Archive-663/samyang7_5mm/ASSETS/PRODUCT/sam7_5_product (2).jpg

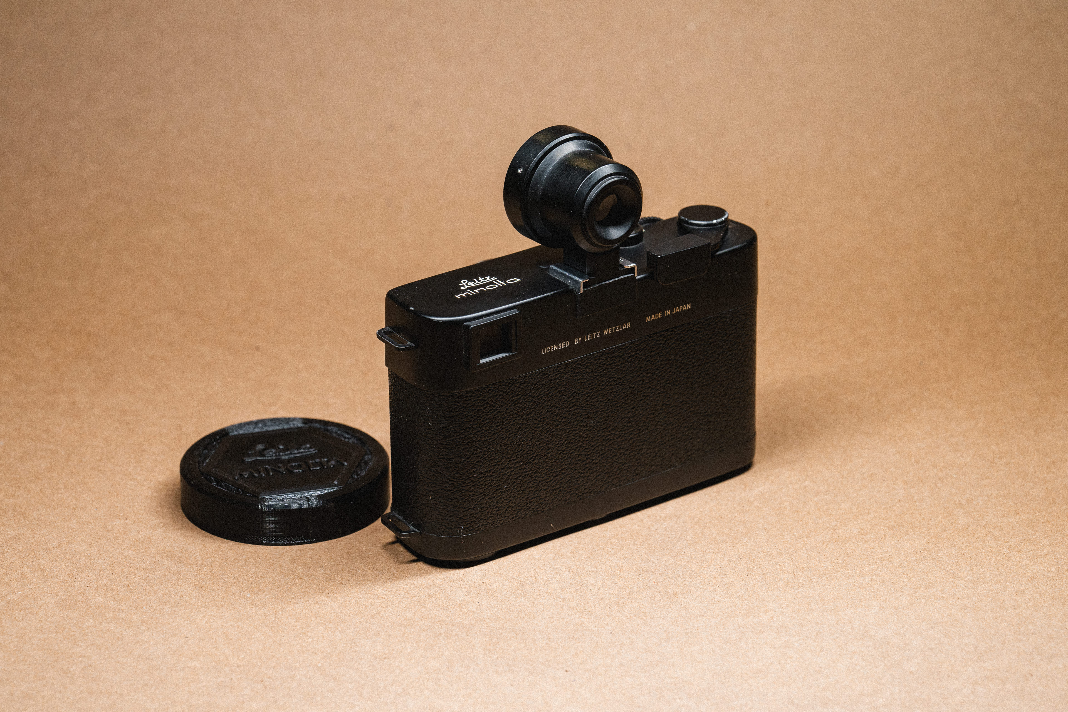
ASSETS/PRODUCT/sam7_5_product (2).jpg
