Archive-663/samyang7_5mm/ASSETS/PRODUCT/sam7_5_product (7).jpg

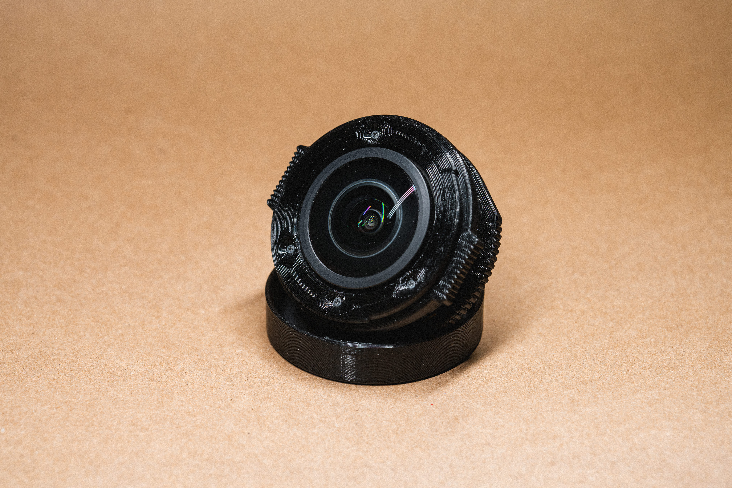
ASSETS/PRODUCT/sam7_5_product (7).jpg
