Archive-663/samyang7_5mm/ASSETS/PRODUCT/sam7_5_product (9).jpg

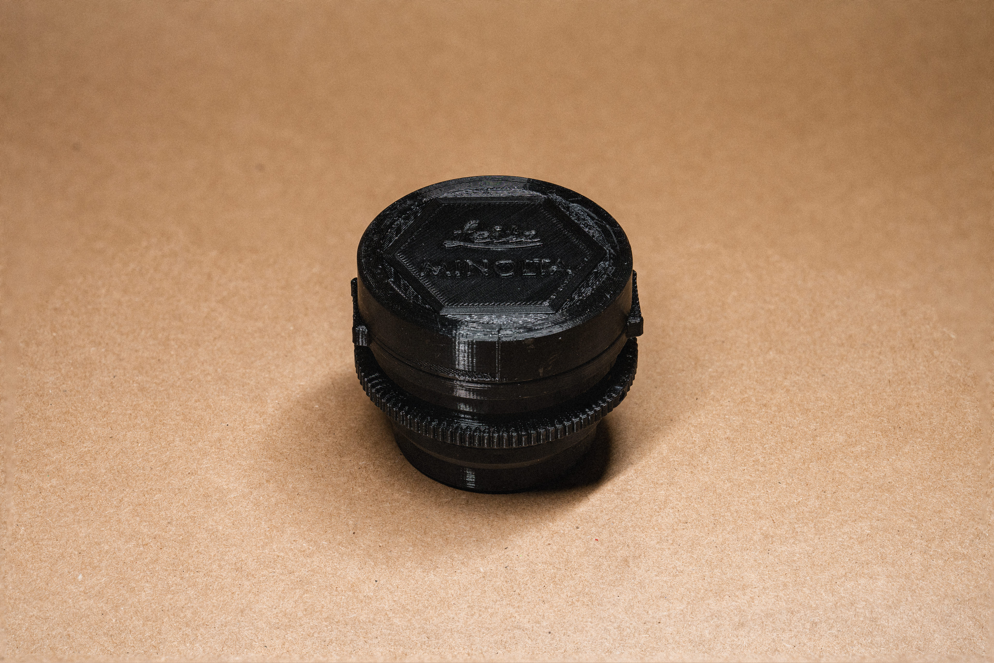
ASSETS/PRODUCT/sam7_5_product (9).jpg
