Archive-663/samyang7_5mm/ASSETS/PRODUCT/sam7_5_product (10).jpg

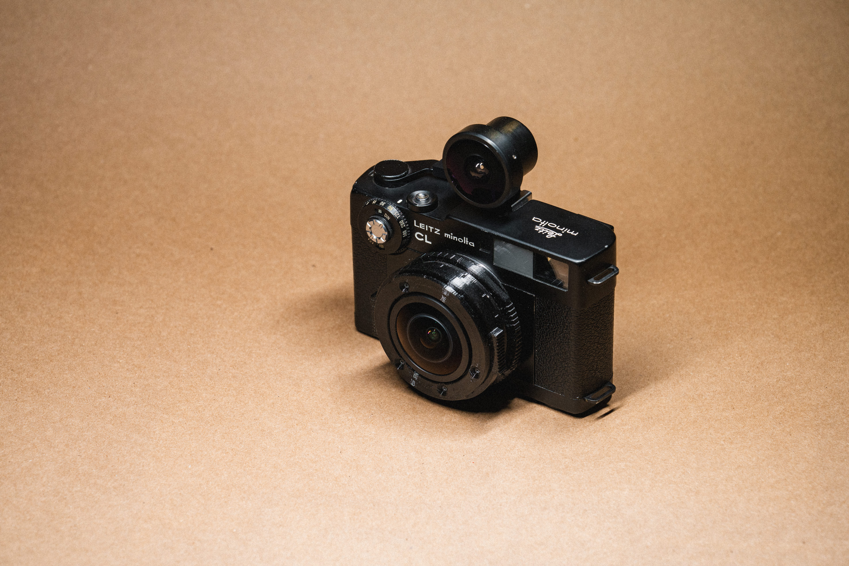
ASSETS/PRODUCT/sam7_5_product (10).jpg
