Archive-663/samyang7_5mm/ASSETS/SAMPLE/sam7_5_sample (22).jpg

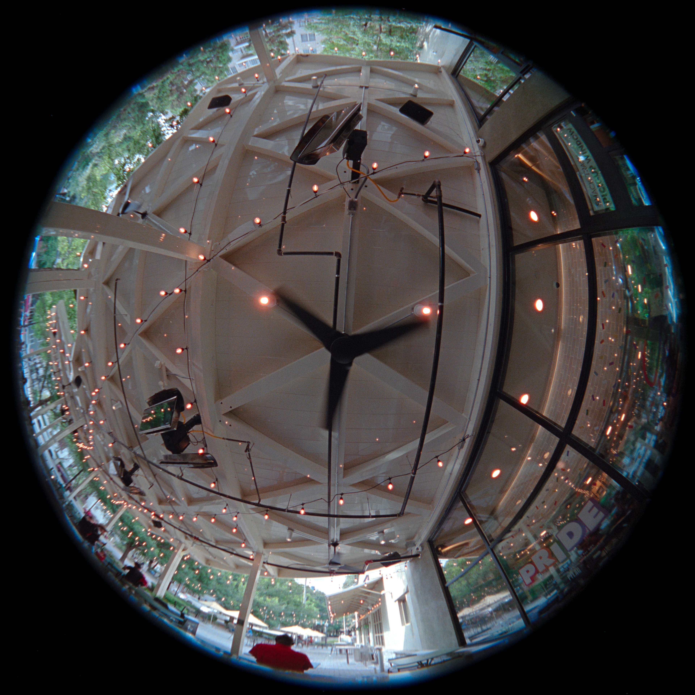
ASSETS/SAMPLE/sam7_5_sample (22).jpg
