Archive-663/samyang7_5mm/viewFinder/STL/Lemuro Fisheye/forPrint/sam7_5_MFT-LM_viewFinderCap_lemuroFisheye_forPrint.stl

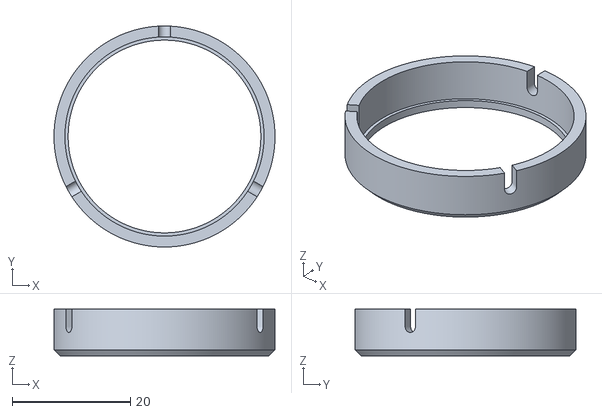
[picture p45: CAD file, 2023-12-08]
viewFinder/STL/Lemuro Fisheye/forPrint/sam7_5_MFT-LM_viewFinderCap_lemuroFisheye_forPrint.stl
37.4 x 37.4 x 7.88
