Archive-663/samyang7_5mm/viewFinder/STL/Standard/sam7_5_MFT-LM_viewFinderColdShoe.stl

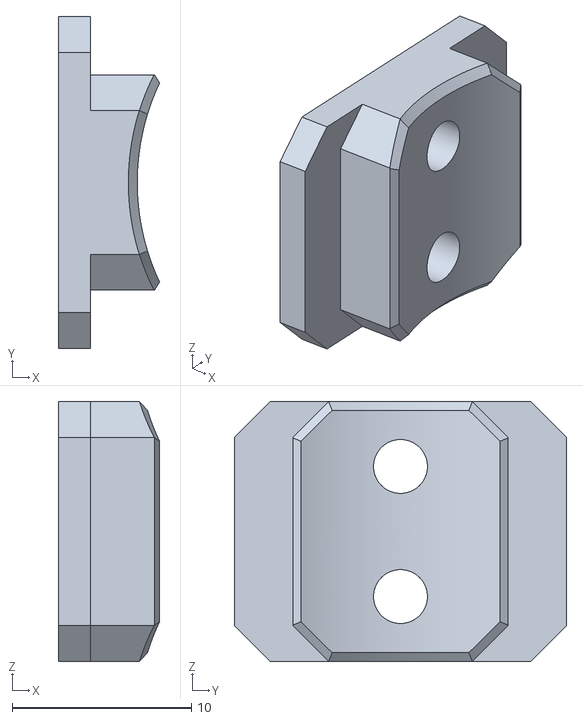
[picture p46: CAD file, 2023-12-08]
viewFinder/STL/Standard/sam7_5_MFT-LM_viewFinderColdShoe.stl
5.64 x 18.5 x 14.5
