Archive-663/samyang7_5mm/sam7_5_MFT-LM_rehousing/STEP/sam7_5_MFT-LM_rearCap_LM.stp

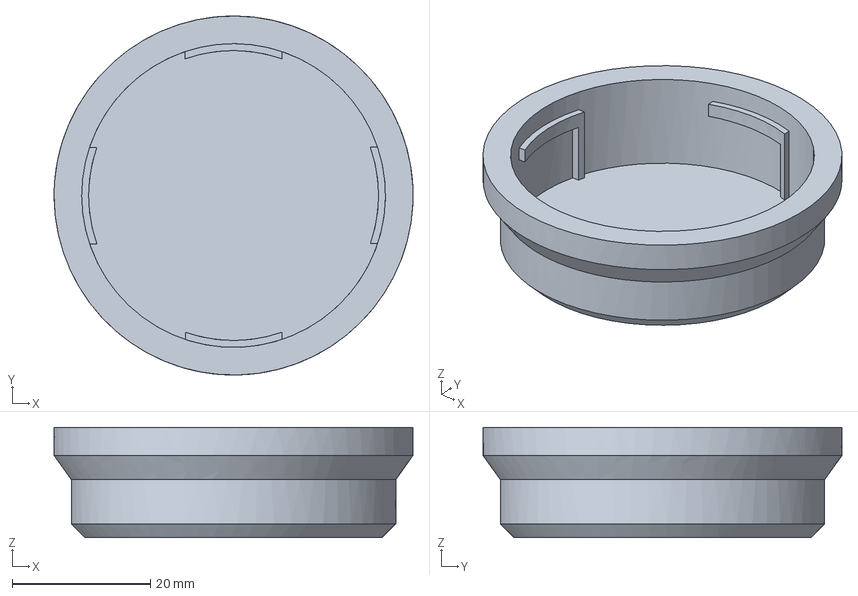
[picture p47: CAD file, 2023-12-08]
sam7_5_MFT-LM_rehousing/STEP/sam7_5_MFT-LM_rearCap_LM.stp
52.0 x 52.0 x 16.0 mm
