Archive-663/samyang7_5mm/viewFinder/STEP/Death Lens Fisheye/forPrint/sam7_5_viewFinderColdShoe_deathLensFisheye_forPrint.stp

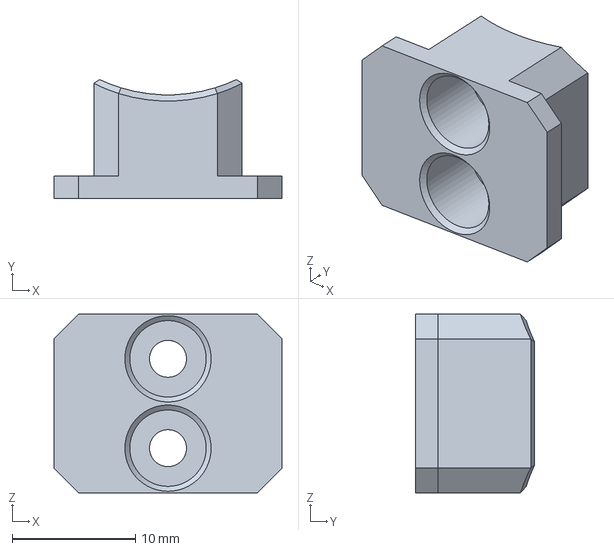
[picture p48: CAD file, 2023-12-08]
viewFinder/STEP/Death Lens Fisheye/forPrint/sam7_5_viewFinderColdShoe_deathLensFisheye_forPrint.stp
18.5 x 9.64 x 14.5 mm
