Archive-663/samyang7_5mm/viewFinder/STEP/Lemuro Fisheye/forCNC/sam7_5_viewFinderBody_lemuroFisheye_forCNC.stp

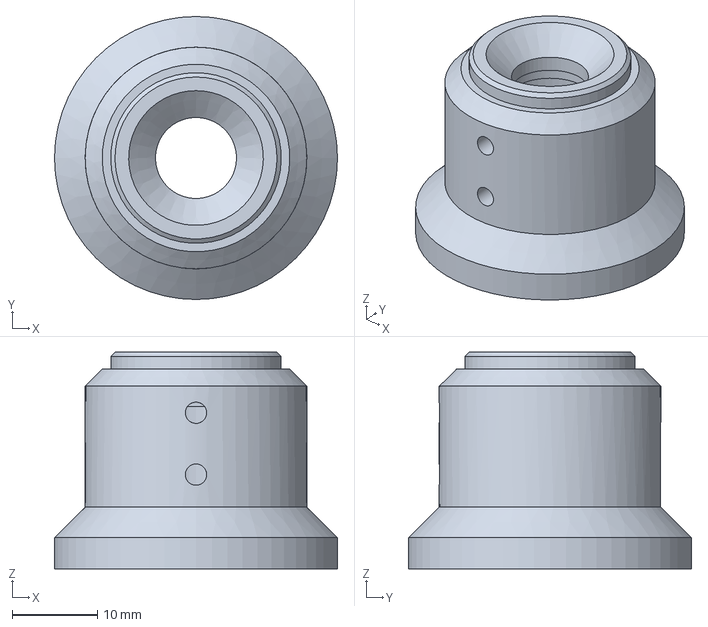
[picture p49: CAD file, 2023-12-08]
viewFinder/STEP/Lemuro Fisheye/forCNC/sam7_5_viewFinderBody_lemuroFisheye_forCNC.stp
33.2 x 33.2 x 25.5 mm
