Archive-663/samyang7_5mm/viewFinder/STEP/Lemuro Fisheye/forPrint/sam7_5_viewFinderColdShoe_lemuroFisheye_forPrint.stp

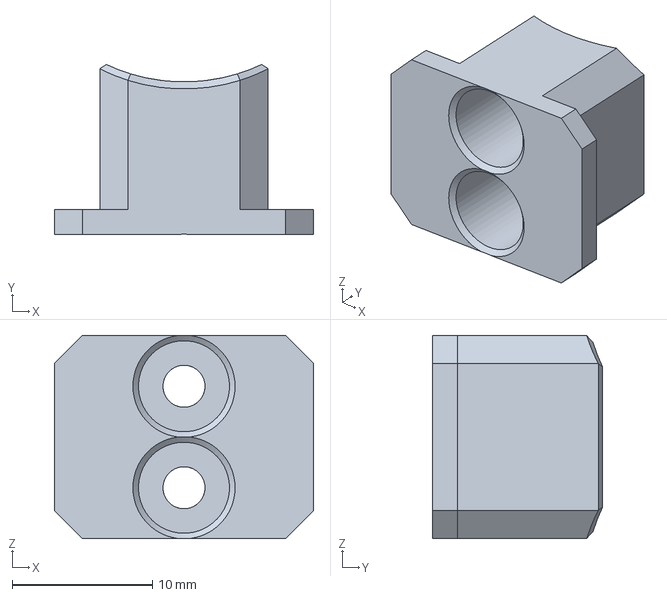
[picture p50: CAD file, 2023-12-08]
viewFinder/STEP/Lemuro Fisheye/forPrint/sam7_5_viewFinderColdShoe_lemuroFisheye_forPrint.stp
18.5 x 12.1 x 14.5 mm
