Archive-663/samyang7_5mm/viewFinder/STEP/Standard/sam7_5_viewFinderBody_standard.stp

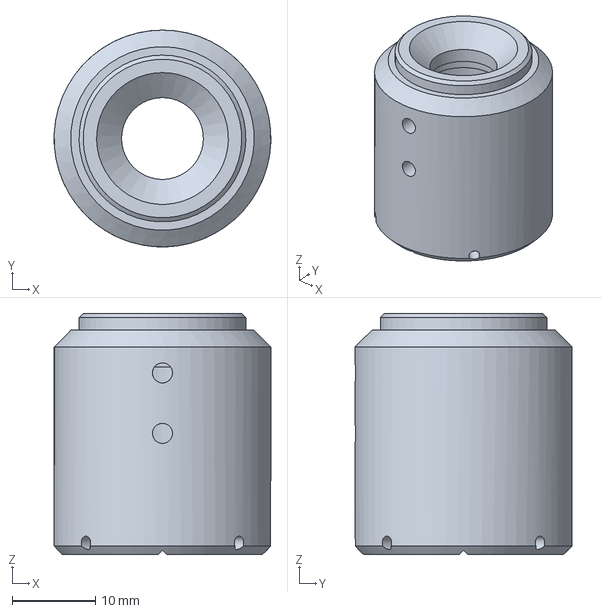
[picture p51: CAD file, 2023-12-08]
viewFinder/STEP/Standard/sam7_5_viewFinderBody_standard.stp
26.0 x 26.0 x 28.9 mm
