Archive-663/samyang7_5mm/viewFinder/STL/Standard/sam7_5_MFT-LM_viewFinder_standard.3mf

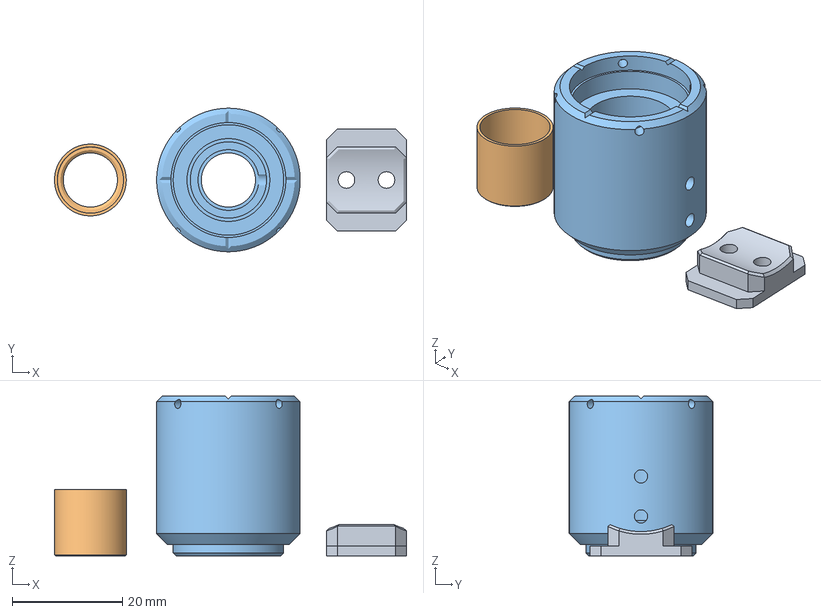
[picture p52: CAD file, 2023-12-08]
viewFinder/STL/Standard/sam7_5_MFT-LM_viewFinder_standard.3mf
63.7 x 26.0 x 28.9 mm
sam7_5_MFT-LM_viewFinderColdShoe.stl
sam7_5_MFT-LM_viewFinder_collar_glassElement.stl
sam7_5_MFT-LM_viewFinderBody_standard.stl
