Archive-663/samyang7_5mm/sam7_5_MFT-LM_rehousing/STEP/sam7_5_MFT-LM_facePlate.stp

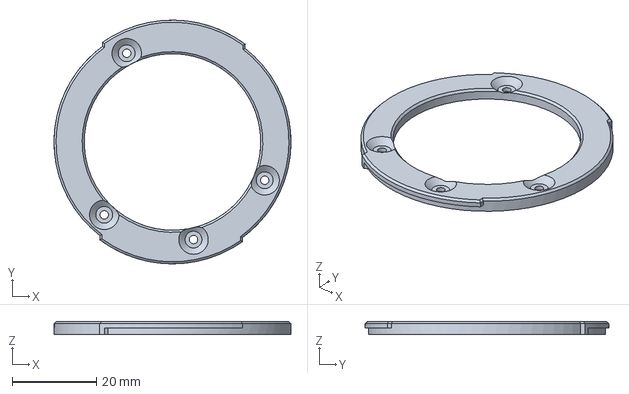
[picture p53: CAD file, 2023-12-08]
sam7_5_MFT-LM_rehousing/STEP/sam7_5_MFT-LM_facePlate.stp
56.4 x 58.0 x 3.10 mm
