Archive-663/samyang7_5mm/viewFinder/STL/Death Lens Fisheye/forPrint/sam7_5_MFT-LM_viewFinderBody_deathLensFisheye_forPrint.stl

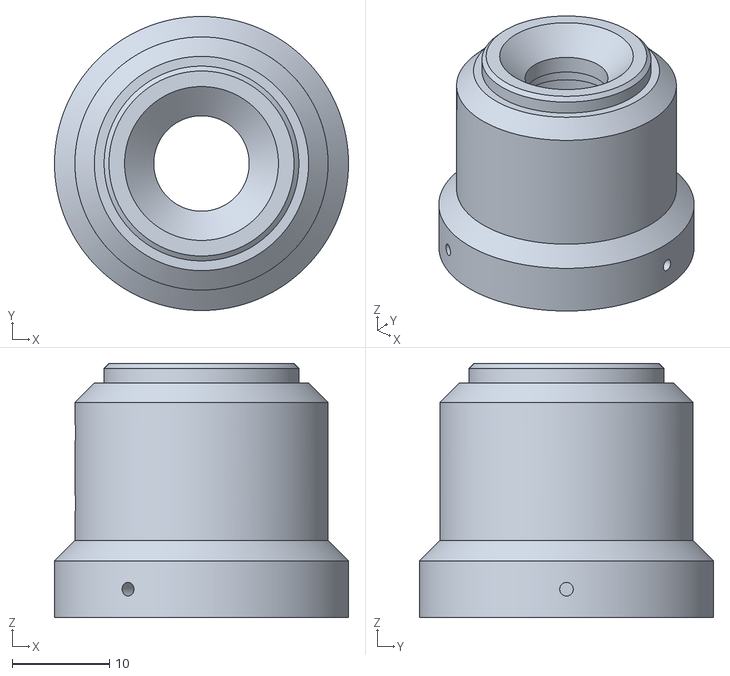
[picture p54: CAD file, 2023-12-08]
viewFinder/STL/Death Lens Fisheye/forPrint/sam7_5_MFT-LM_viewFinderBody_deathLensFisheye_forPrint.stl
30.2 x 30.2 x 26.1
