Archive-663/samyang7_5mm/viewFinder/STL/Lemuro Fisheye/forPrint/sam7_5_MFT-LM_viewFinder_lemuroFisheye.3mf

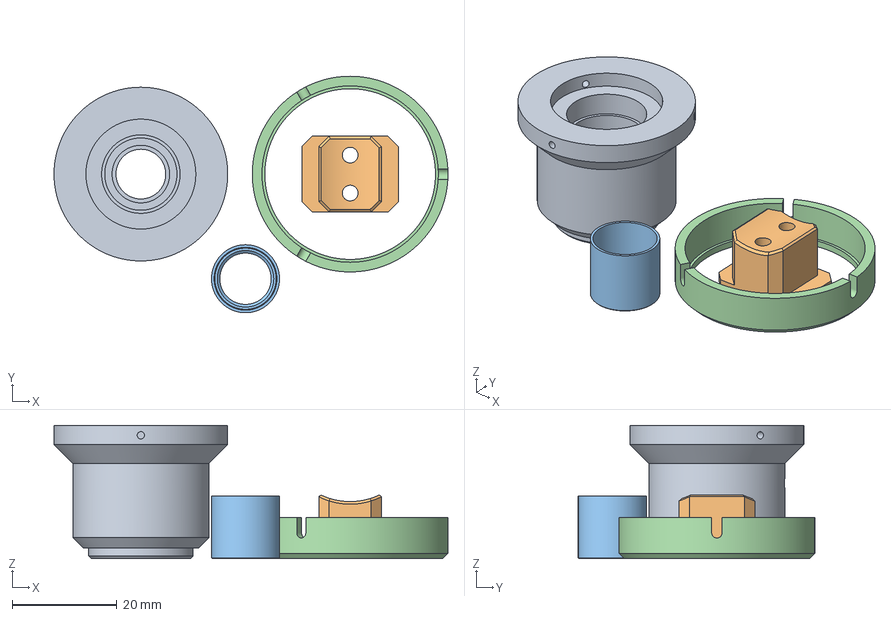
[picture p55: CAD file, 2023-12-08]
viewFinder/STL/Lemuro Fisheye/forPrint/sam7_5_MFT-LM_viewFinder_lemuroFisheye.3mf
75.3 x 45.2 x 25.4 mm
sam7_5_MFT-LM_viewFinderBody_lemuroFisheye_forPrint.stl
sam7_5_MFT-LM_viewFinderColdShoe_lemuroFisheye_forPrint.stl
sam7_5_MFT-LM_viewFinder_collar_glassElement.stl
sam7_5_MFT-LM_viewFinderCap_lemuroFisheye_forPrint.stl
