Archive-663/samyang7_5mm/sam7_5_MFT-LM_rehousing/STEP/sam7_5_MFT-LM_apertureArmBuck.stp

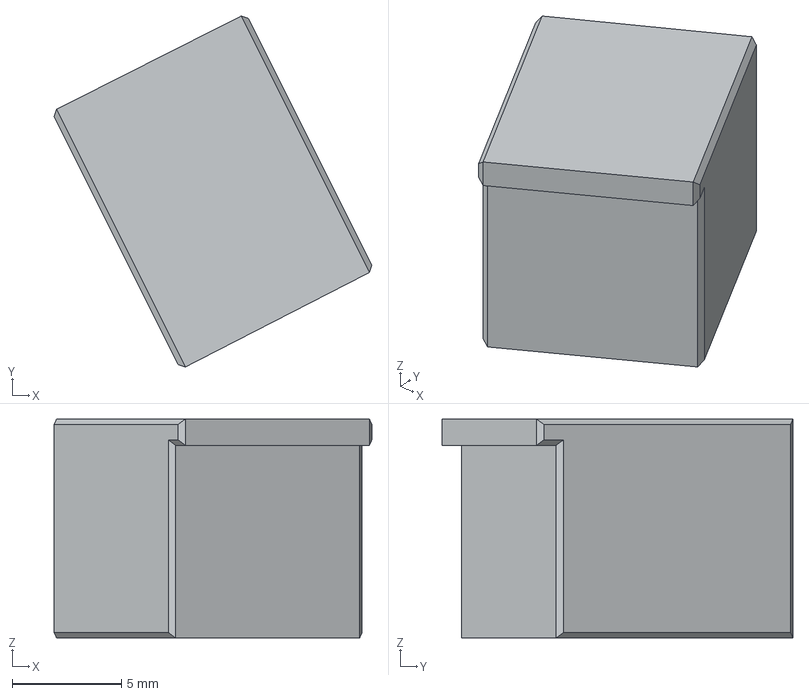
[picture p56: CAD file, 2023-12-08]
sam7_5_MFT-LM_rehousing/STEP/sam7_5_MFT-LM_apertureArmBuck.stp
14.5 x 16.0 x 10.00 mm
