Archive-663/samyang7_5mm/viewFinder/STL/Death Lens Fisheye/forPrint/sam7_5_MFT-LM_viewFinder_deathLensFisheye.3mf

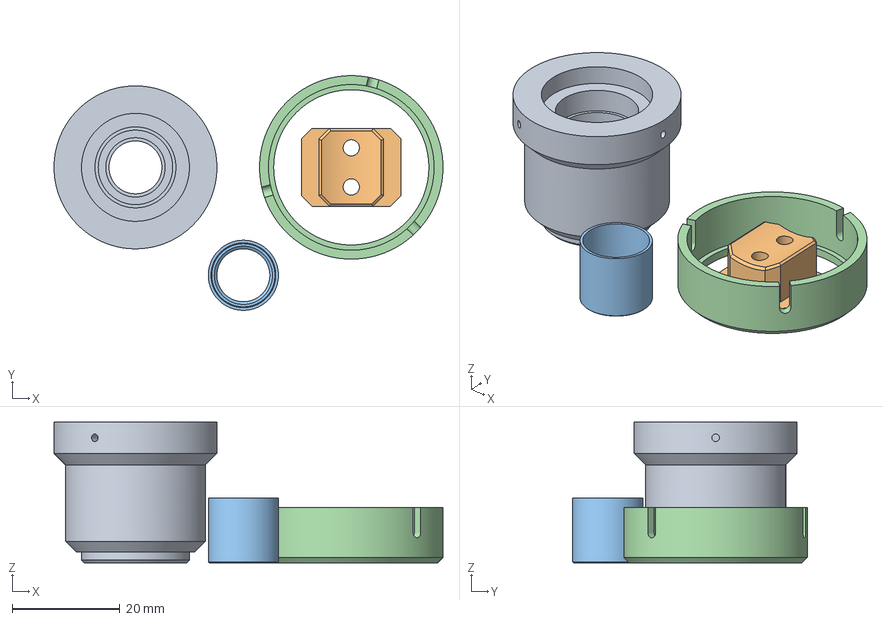
[picture p57: CAD file, 2023-12-08]
viewFinder/STL/Death Lens Fisheye/forPrint/sam7_5_MFT-LM_viewFinder_deathLensFisheye.3mf
72.1 x 43.5 x 26.1 mm
sam7_5_MFT-LM_viewFinderBody_deathLensFisheye_forPrint.stl
sam7_5_MFT-LM_viewFinderColdShoe_deathLensFisheye_forPrint.stl
sam7_5_MFT-LM_viewFinder_collar_glassElement.stl
sam7_5_MFT-LM_viewFinderCap_deathLensFisheye_forPrint.stl
