Archive-663/samyang7_5mm/sam7_5_MFT-LM_rehousing/STEP/sam7_5_MFT-LM_lensCap.stp

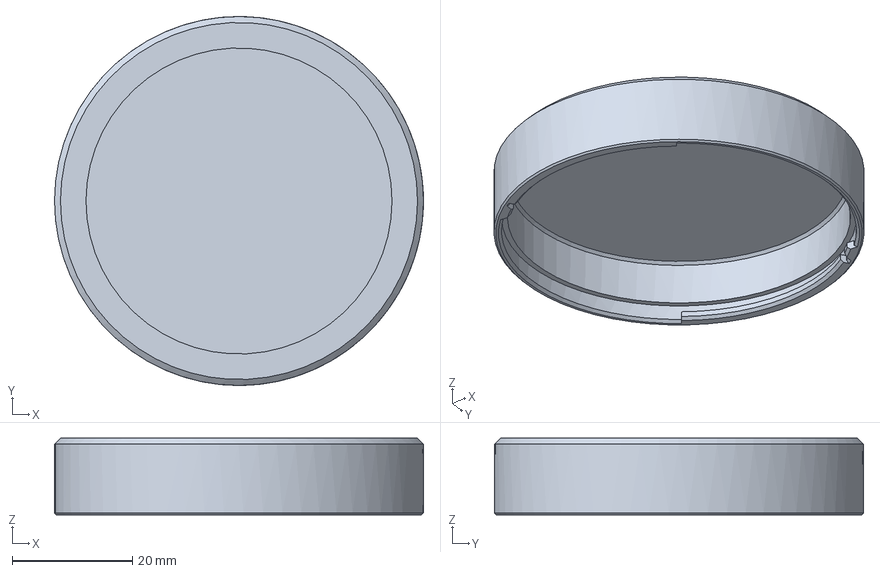
[picture p59: CAD file, 2023-12-08]
sam7_5_MFT-LM_rehousing/STEP/sam7_5_MFT-LM_lensCap.stp
61.5 x 61.5 x 12.8 mm
