Archive-663/samyang7_5mm/sam7_5_MFT-LM_rehousing/STEP/sam7_5_MFT-LM_indicatorRing.stp

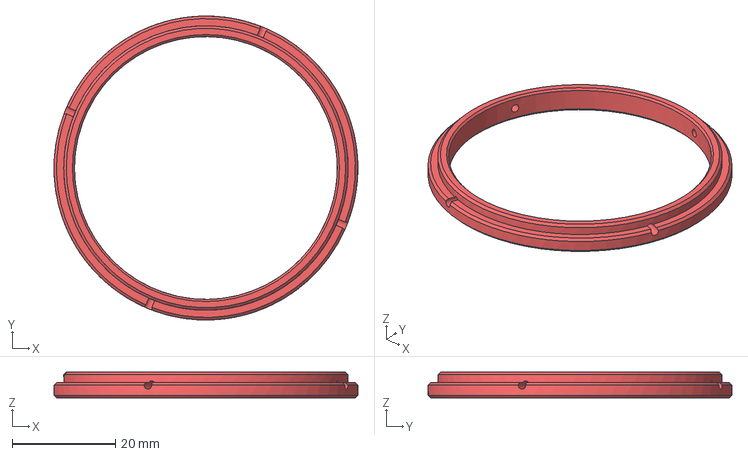
[picture p60: CAD file, 2023-12-08]
sam7_5_MFT-LM_rehousing/STEP/sam7_5_MFT-LM_indicatorRing.stp
59.0 x 59.0 x 5.00 mm
