Archive-663/samyang7_5mm/sam7_5_MFT-LM_rehousing/STEP/sam7_5_MFT-LM_apertureArmTemplate.stp

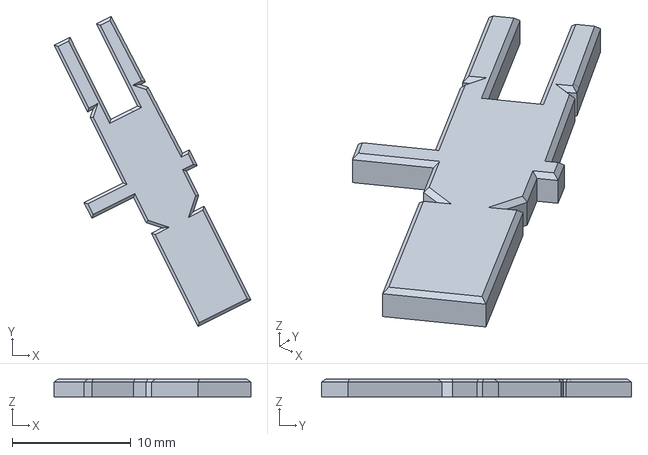
[picture p62: CAD file, 2023-12-08]
sam7_5_MFT-LM_rehousing/STEP/sam7_5_MFT-LM_apertureArmTemplate.stp
16.6 x 26.2 x 1.50 mm
