Archive-663/samyang7_5mm/sam7_5_MFT-LM_rehousing/STEP/sam7_5_MFT-LM_lensCapNameplate.stp

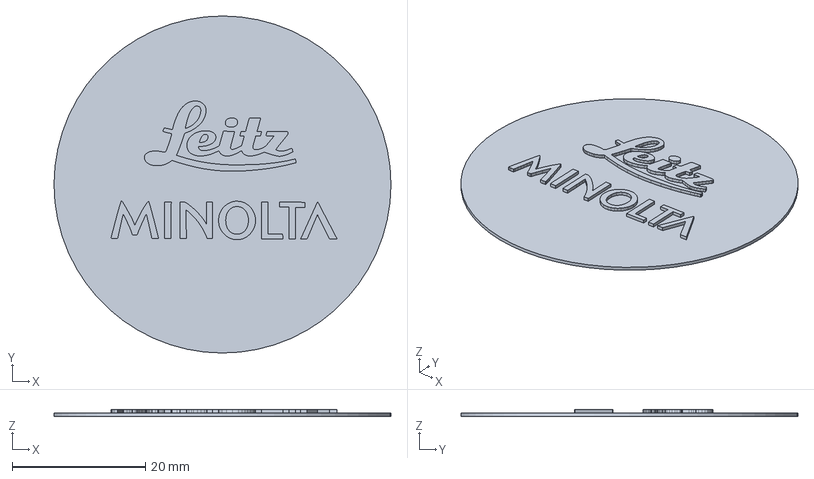
[picture p66: CAD file, 2023-12-08]
sam7_5_MFT-LM_rehousing/STEP/sam7_5_MFT-LM_lensCapNameplate.stp
50.5 x 50.5 x 1.00 mm
